HecVelaz/Sistema-de-adquisicion-y-monitoreo-de-nivel/documentos/Diseño Mecánico/sensor/Soporte.SLDPRT

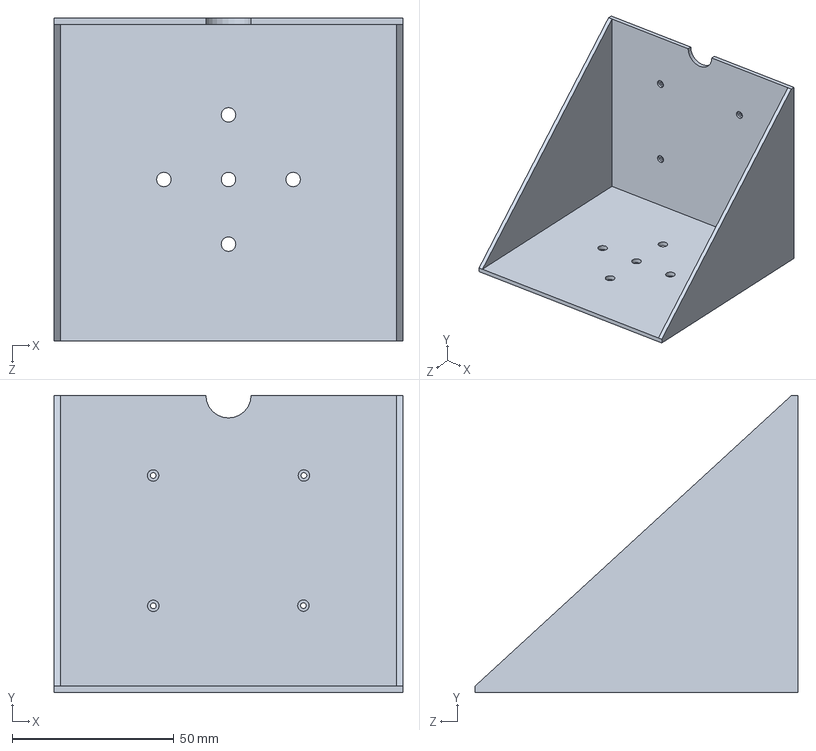
[picture p91: CAD file, 2026-09-18]
documentos/Diseño Mecánico/sensor/Soporte.SLDPRT
108.0 x 92.0 x 100.0 mm
