HecVelaz/Sistema-de-adquisicion-y-monitoreo-de-nivel/documentos/Diseño Mecánico/Caja/cable4.SLDPRT

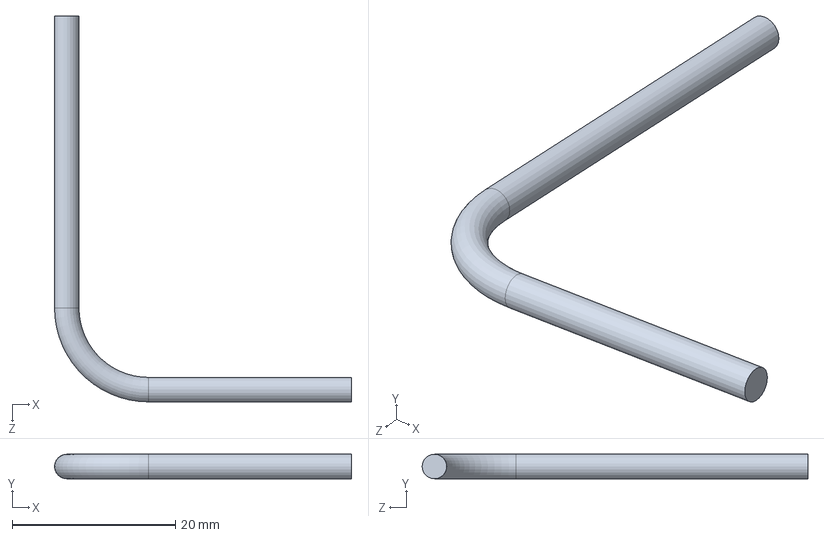
[picture p92: CAD file, 2026-09-18]
documentos/Diseño Mecánico/Caja/cable4.SLDPRT
36.3 x 3.00 x 47.2 mm
