HecVelaz/Sistema-de-adquisicion-y-monitoreo-de-nivel/documentos/Diseño Mecánico/Caja/moden.SLDPRT

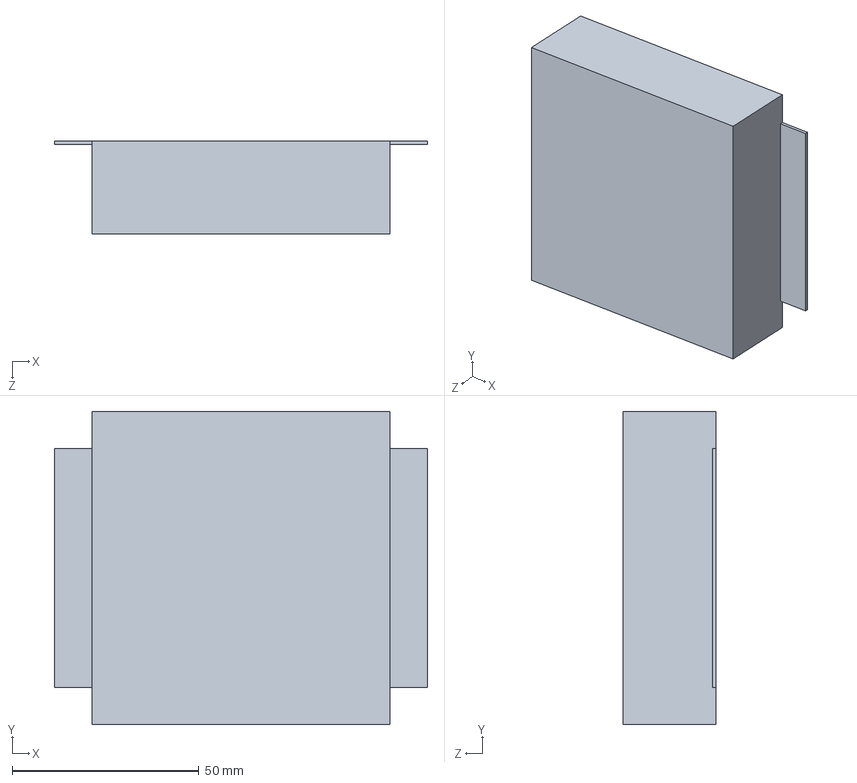
[picture p93: CAD file, 2026-09-18]
documentos/Diseño Mecánico/Caja/moden.SLDPRT
100.0 x 84.0 x 25.0 mm
