HecVelaz/Sistema-de-adquisicion-y-monitoreo-de-nivel/documentos/Diseño Mecánico/sensor/Ensamblaje_sensor.SLDASM

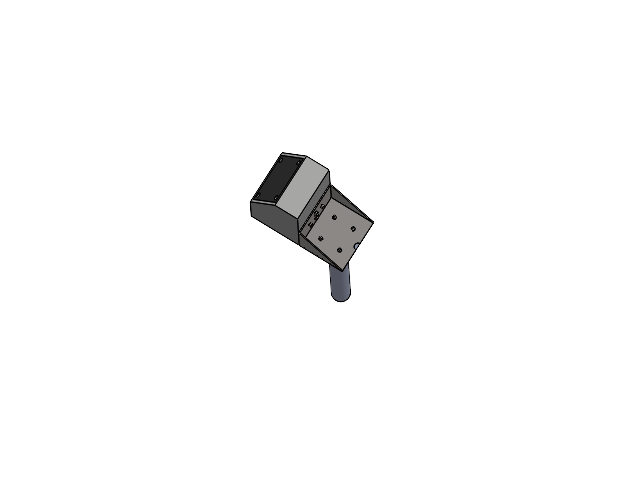
[picture p94: CAD file, 2026-09-18]
documentos/Diseño Mecánico/sensor/Ensamblaje_sensor.SLDASM
Soporte
Screw_DIN_912_M4x10F_A2 x 9
Sensor
Soporte2
