HecVelaz/Sistema-de-adquisicion-y-monitoreo-de-nivel/documentos/Evidencias_Pruebas/capturas/Base_de_datos_servidor.jpg

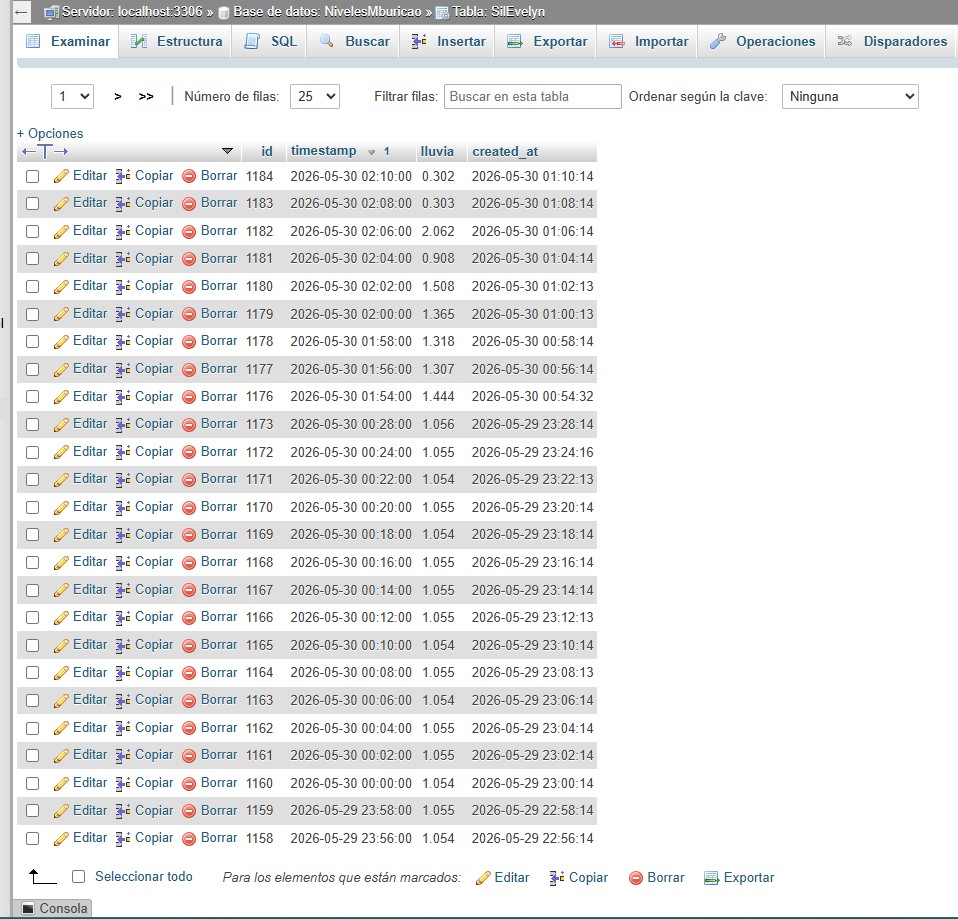
documentos/Evidencias_Pruebas/capturas/Base_de_datos_servidor.jpg
