HecVelaz/Sistema-de-adquisicion-y-monitoreo-de-nivel/documentos/Evidencias_Pruebas/capturas/Placa PCB.jpeg

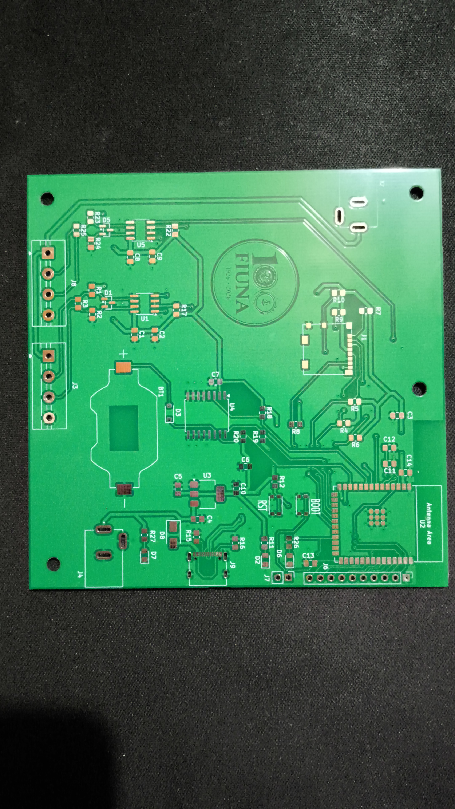
documentos/Evidencias_Pruebas/capturas/Placa PCB.jpeg
