HecVelaz/Sistema-de-adquisicion-y-monitoreo-de-nivel/documentos/Evidencias_Pruebas/capturas/Placa.jpg

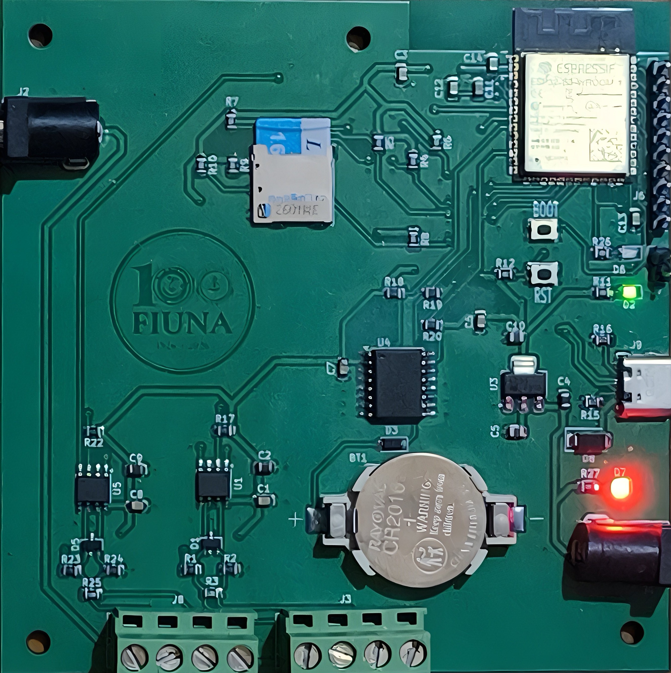
documentos/Evidencias_Pruebas/capturas/Placa.jpg
