HecVelaz/Sistema-de-adquisicion-y-monitoreo-de-nivel/documentos/Evidencias_Pruebas/capturas/servidor_sensor_lectura.jpg

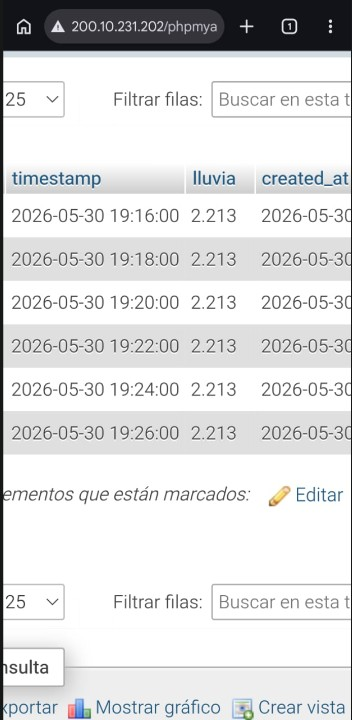
documentos/Evidencias_Pruebas/capturas/servidor_sensor_lectura.jpg
